TeamCSCV/Project-Orologio/Individual/Audio Output (Chathushka)/2nd Stage/Solid Works/Bouton poussoir.SLDPRT

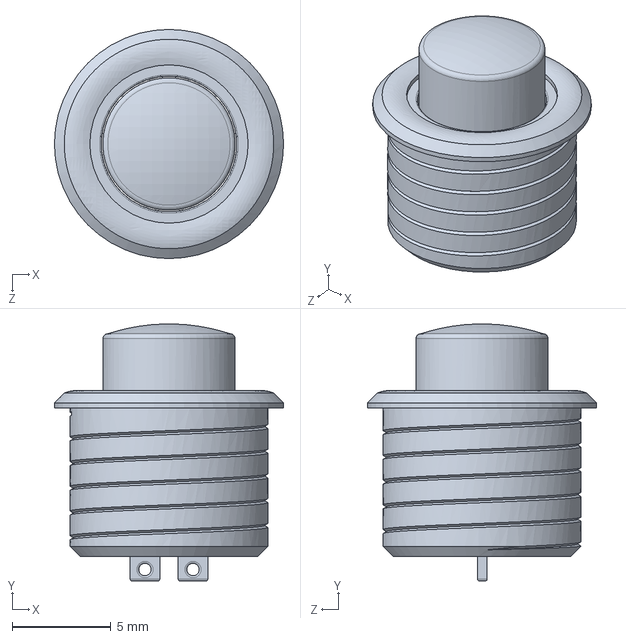
[picture p15: CAD file, 2021-05-29]
Individual/Audio Output (Chathushka)/2nd Stage/Solid Works/Bouton poussoir.SLDPRT
11.6 x 13.0 x 11.6 mm
