TeamCSCV/Project-Orologio/Group/PCB and Schematic/PCB_Project/Models/BC547-B.step

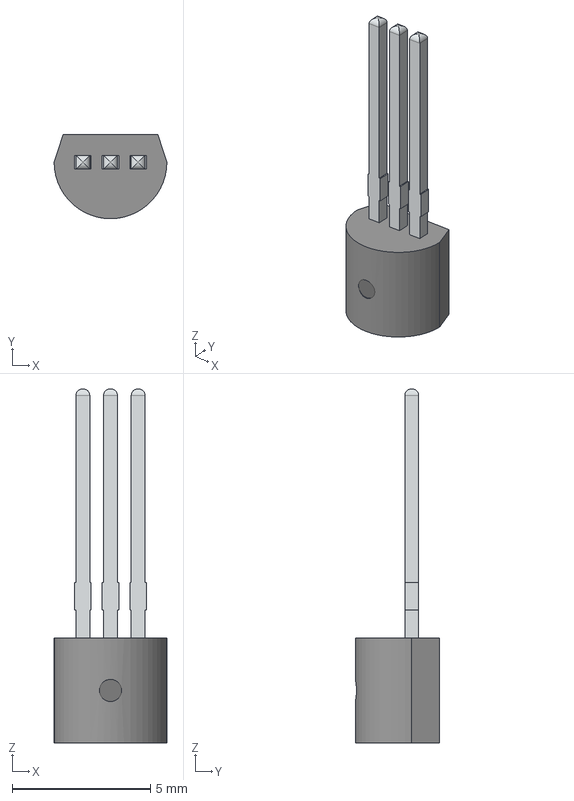
[picture p16: CAD file, 2021-05-29]
Group/PCB and Schematic/PCB_Project/Models/BC547-B.step
4.08 x 3.05 x 12.8 mm
