TeamCSCV/Project-Orologio/Individual/Key Input (Senuri)/Solidworks/9V Battery Holder.SLDPRT

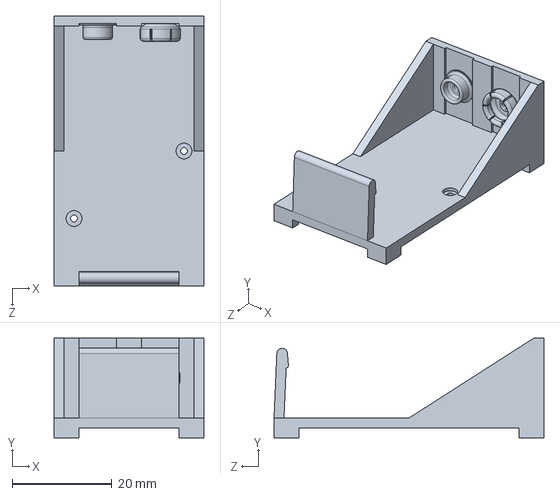
[picture p17: CAD file, 2021-05-29]
Individual/Key Input (Senuri)/Solidworks/9V Battery Holder.SLDPRT
30.0 x 20.0 x 54.0 mm
