TeamCSCV/Project-Orologio/Group/Enclosure/Right Side Arm.STEP

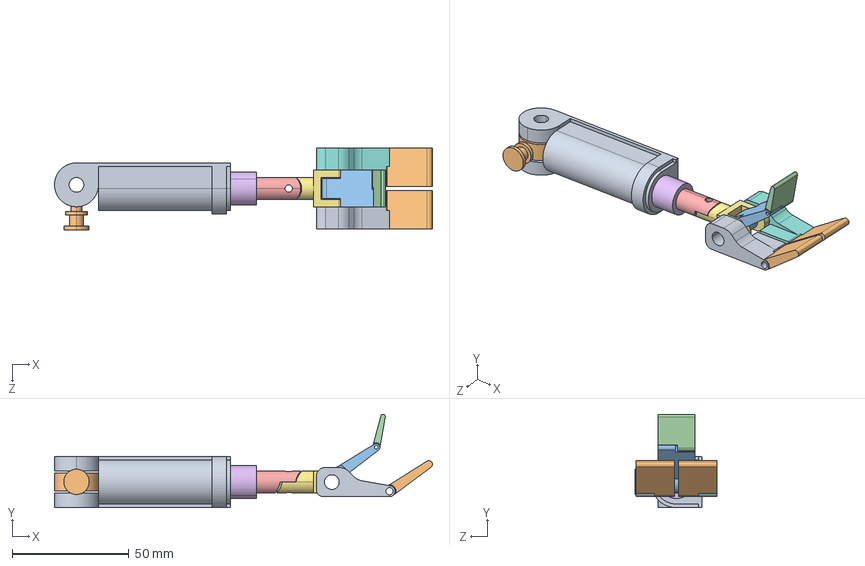
[picture p18: CAD file, 2021-08-09]
Group/Enclosure/Right Side Arm.STEP
161.8 x 40.0 x 34.9 mm
Arm - Main Body
Hand Part 2 x 2
Hand Part 3
Hand Part 4
Hydraulic Arm
Hydraulic Cylinder
Wrist
Hand Part 1
Hand Part 1-2
Sholder
