TeamCSCV/Project-Orologio/Group/PCB and Schematic/PCB_Project/Models/Aluminum_electrolytic_capacitor_radial_D8_H11.5_PinD0.6_Pitch3.5_nominal_black.step

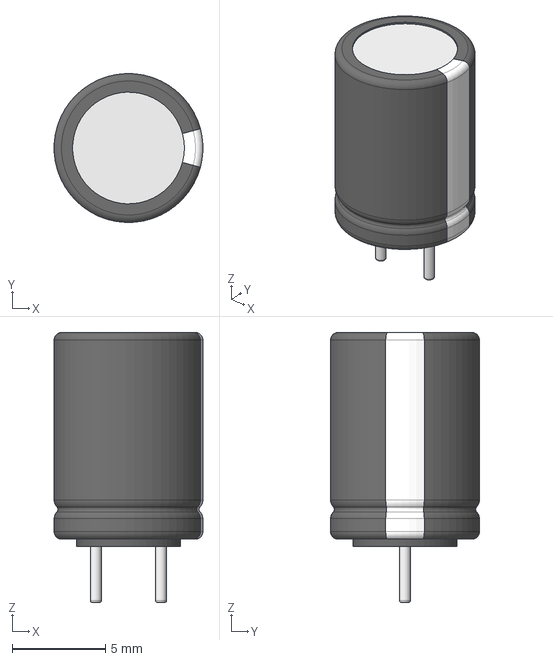
[picture p19: CAD file, 2021-05-29]
Group/PCB and Schematic/PCB_Project/Models/Aluminum_electrolytic_capacitor_radial_D8_H11.5_PinD0.6_Pitch3.5_nominal_black.step
7.99 x 7.99 x 14.5 mm
