TeamCSCV/Project-Orologio/Individual/Key Input (Senuri)/Solidworks/test_bottom.SLDPRT

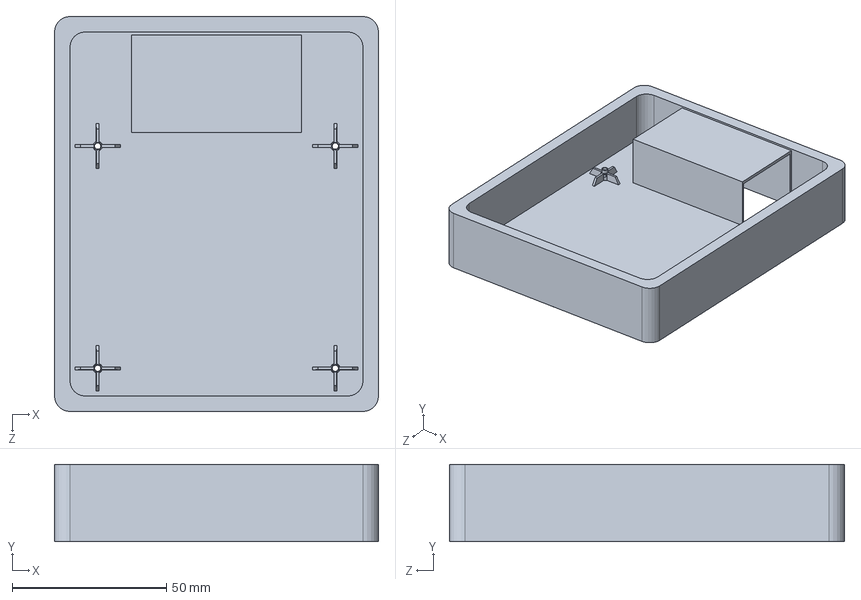
[picture p20: CAD file, 2021-05-29]
Individual/Key Input (Senuri)/Solidworks/test_bottom.SLDPRT
105.0 x 25.0 x 128.0 mm
