TeamCSCV/Project-Orologio/Group/Enclosure/upper part.SLDPRT

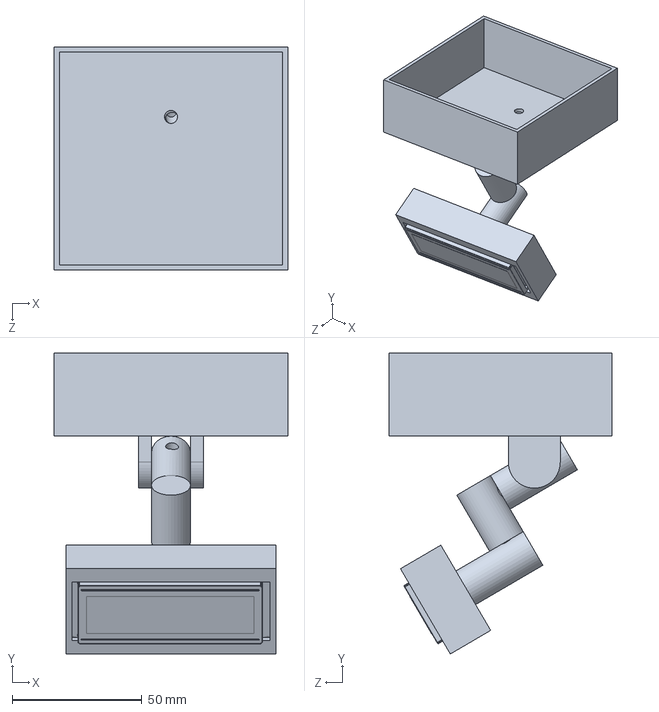
[picture p21: CAD file, 2021-08-09]
Group/Enclosure/upper part.SLDPRT
90.0 x 115.8 x 86.0 mm
