TeamCSCV/Project-Orologio/Group/PCB and Schematic/PCB_Project/Models/L7805ACV.STEP

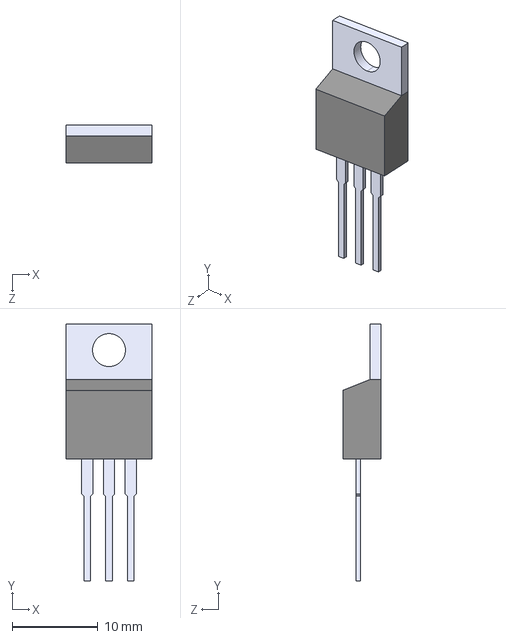
[picture p22: CAD file, 2021-05-29]
Group/PCB and Schematic/PCB_Project/Models/L7805ACV.STEP
10.1 x 30.0 x 4.44 mm
