TeamCSCV/Project-Orologio/Individual/Alarm Timing (Vinuja)/Solidworks enclosure/labProject_micro_top.STEP

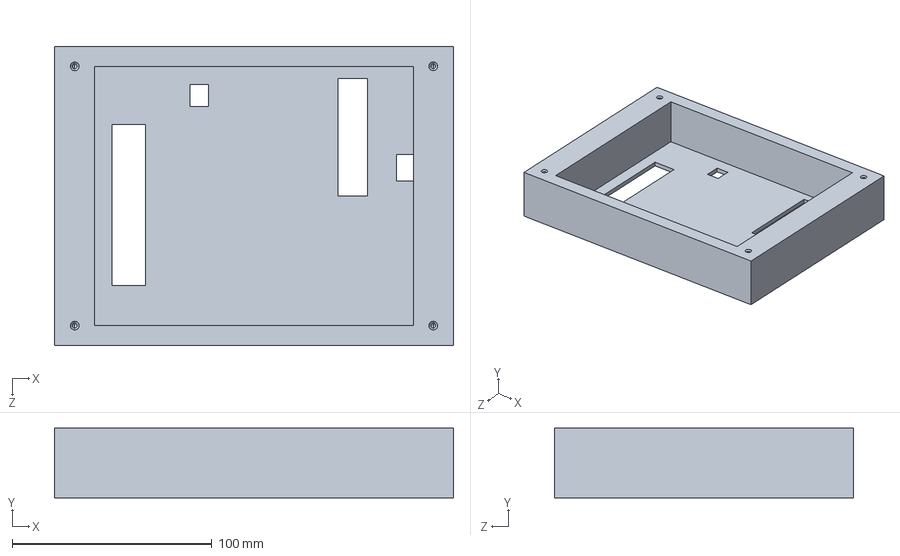
[picture p23: CAD file, 2021-05-29]
Individual/Alarm Timing (Vinuja)/Solidworks enclosure/labProject_micro_top.STEP
200.0 x 35.0 x 150.0 mm
