TeamCSCV/Project-Orologio/Individual/Key Input (Senuri)/Solidworks/Keypad 3x4.STEP

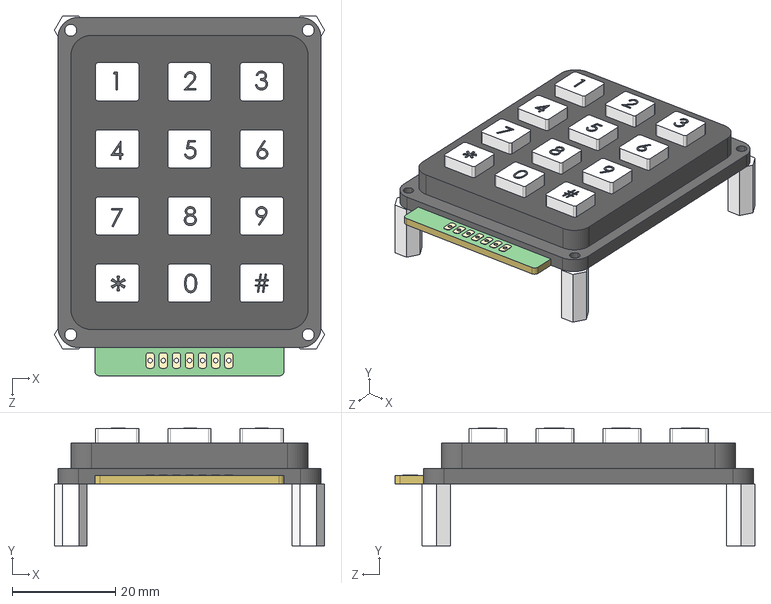
[picture p24: CAD file, 2021-05-29]
Individual/Key Input (Senuri)/Solidworks/Keypad 3x4.STEP
52.4 x 22.8 x 69.8 mm
