TeamCSCV/Project-Orologio/Group/Enclosure/TMB12A05.step.SLDPRT

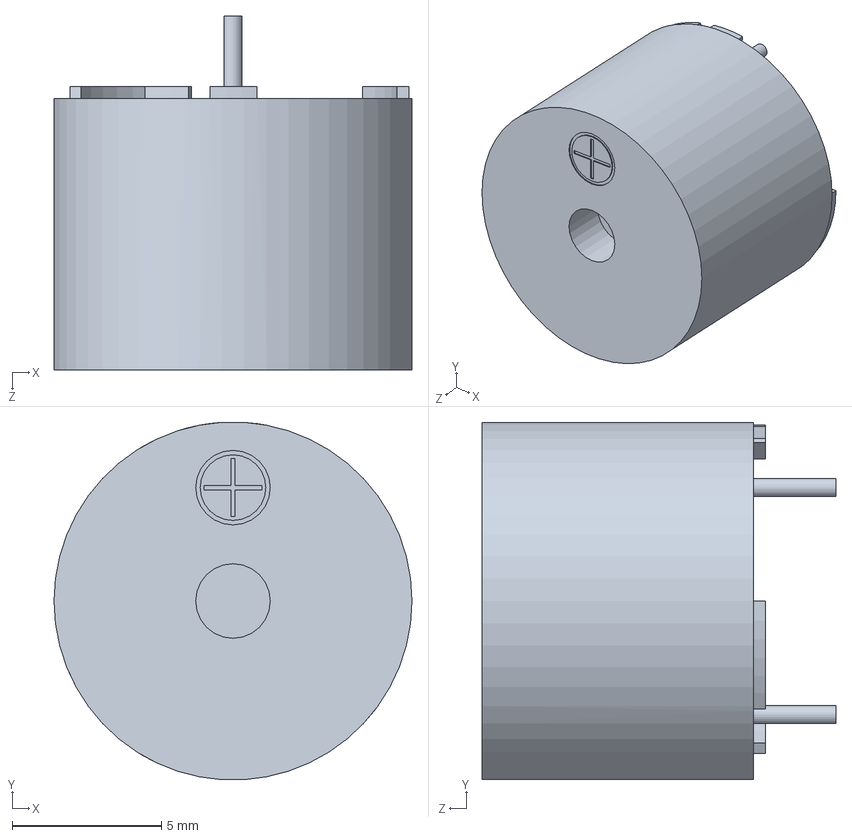
[picture p25: CAD file, 2021-08-09]
Group/Enclosure/TMB12A05.step.SLDPRT
12.0 x 12.0 x 11.9 mm
