TeamCSCV/Project-Orologio/Group/PCB and Schematic/PCB_Project/Models/atmega328p-pu.stp

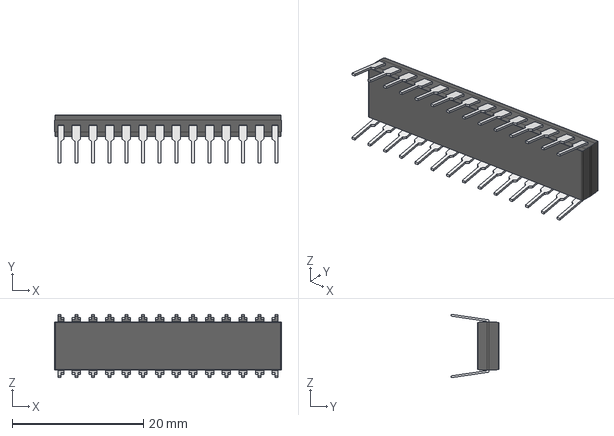
[picture p26: CAD file, 2021-05-29]
Group/PCB and Schematic/PCB_Project/Models/atmega328p-pu.stp
34.6 x 7.30 x 9.68 mm
