TeamCSCV/Project-Orologio/Individual/Alarm Timing (Vinuja)/Solidworks enclosure/labProject_micro_bottom.STEP

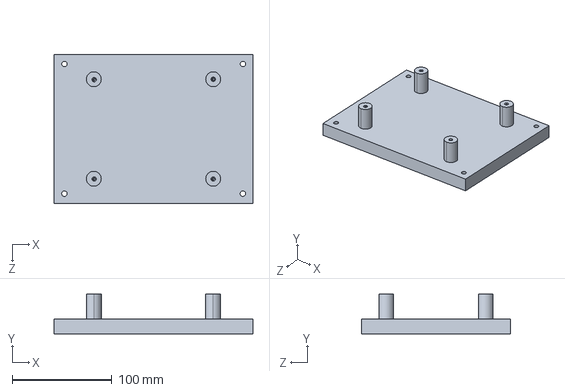
[picture p27: CAD file, 2021-05-29]
Individual/Alarm Timing (Vinuja)/Solidworks enclosure/labProject_micro_bottom.STEP
200.0 x 40.0 x 150.0 mm
