TeamCSCV/Project-Orologio/Group/PCB and Schematic/PCB_Project/Models/1N4001--3DModel-STEP-56544.STEP

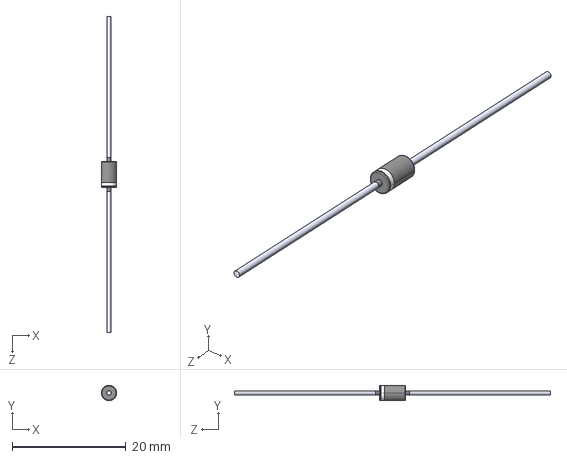
[picture p28: CAD file, 2021-05-29]
Group/PCB and Schematic/PCB_Project/Models/1N4001--3DModel-STEP-56544.STEP
2.69 x 2.69 x 55.4 mm
