TeamCSCV/Project-Orologio/Individual/Display (Chamith)/Solidworks file/button_head.SLDPRT

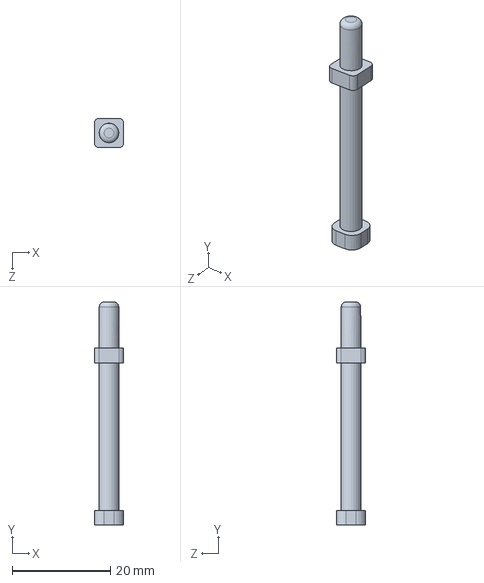
[picture p29: CAD file, 2021-05-31]
Individual/Display (Chamith)/Solidworks file/button_head.SLDPRT
6.00 x 45.5 x 6.00 mm
