TeamCSCV/Project-Orologio/Individual/Display (Chamith)/Solidworks file/top1.SLDPRT

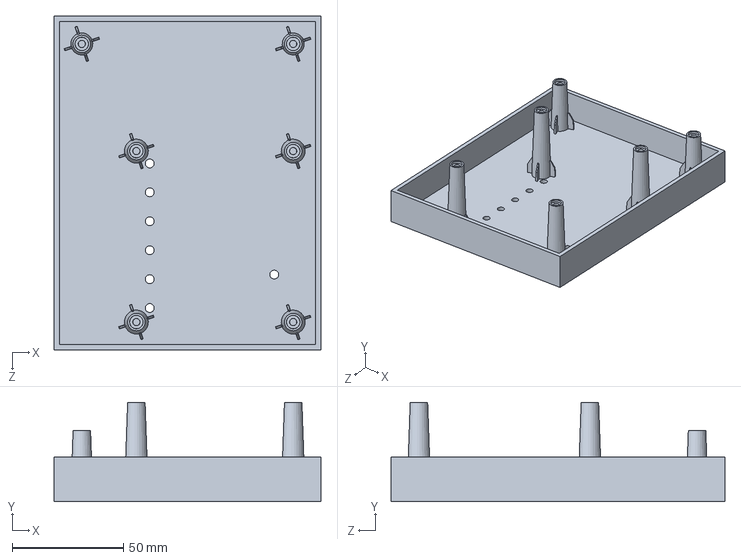
[picture p30: CAD file, 2021-05-31]
Individual/Display (Chamith)/Solidworks file/top1.SLDPRT
120.0 x 44.6 x 150.0 mm
