TeamCSCV/Project-Orologio/Individual/Display (Chamith)/Solidworks file/base1.SLDPRT

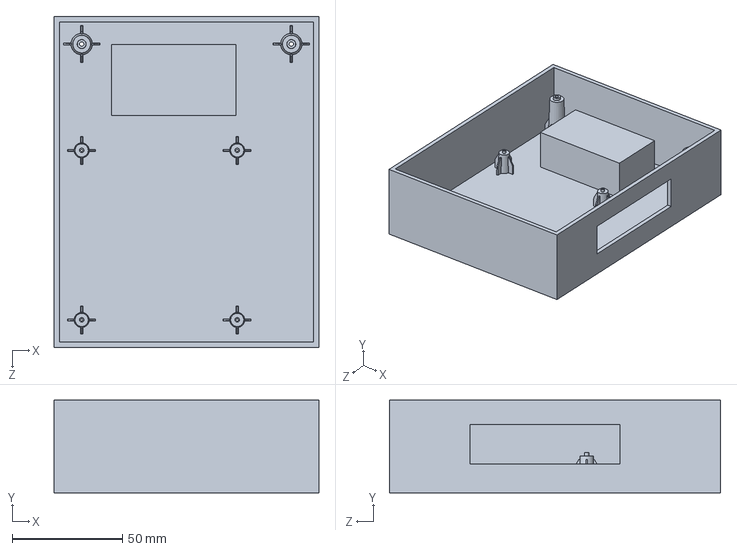
[picture p31: CAD file, 2021-05-31]
Individual/Display (Chamith)/Solidworks file/base1.SLDPRT
120.0 x 42.0 x 150.0 mm
