TeamCSCV/Project-Orologio/Individual/Display (Chamith)/Solidworks file/support to LCD.SLDPRT

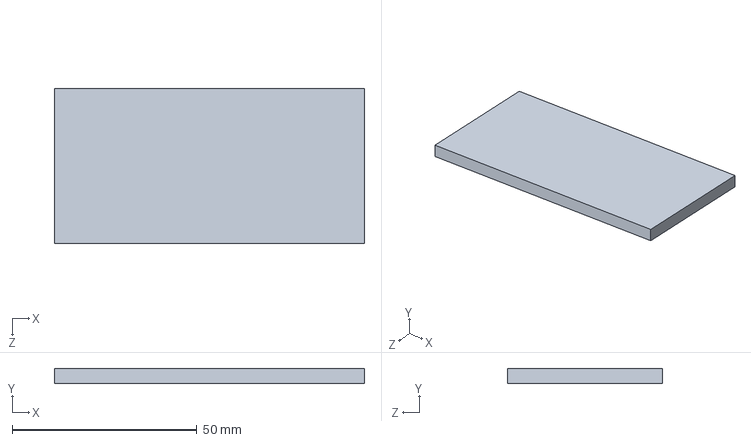
[picture p32: CAD file, 2021-05-31]
Individual/Display (Chamith)/Solidworks file/support to LCD.SLDPRT
84.0 x 4.00 x 42.0 mm
