TeamCSCV/Project-Orologio/Group/Enclosure/wheel.STEP

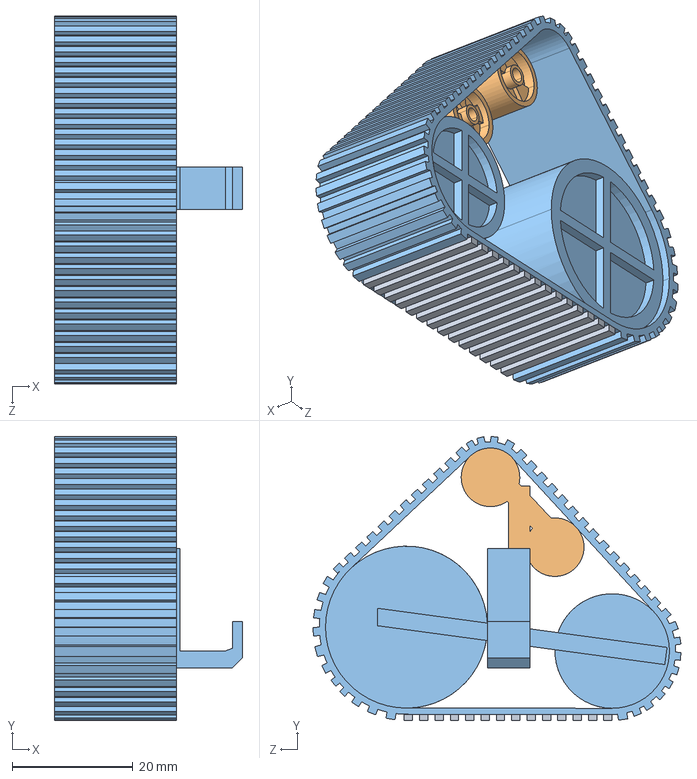
[picture p33: CAD file, 2021-08-04]
Group/Enclosure/wheel.STEP
31.1 x 47.0 x 60.9 mm
