TeamCSCV/Project-Orologio/Group/Enclosure/Matrix Keypad 12 Key (4X3).SLDPRT

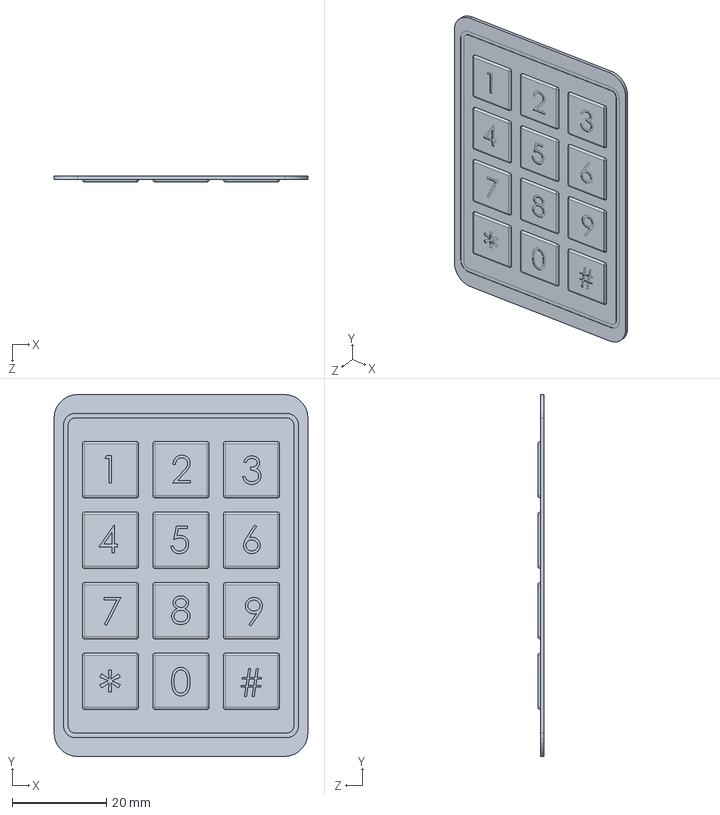
[picture p34: CAD file, 2021-08-04]
Group/Enclosure/Matrix Keypad 12 Key (4X3).SLDPRT
54.0 x 77.0 x 1.31 mm
