TeamCSCV/Project-Orologio/Group/Enclosure/BATTARY HOLDER.SLDPRT

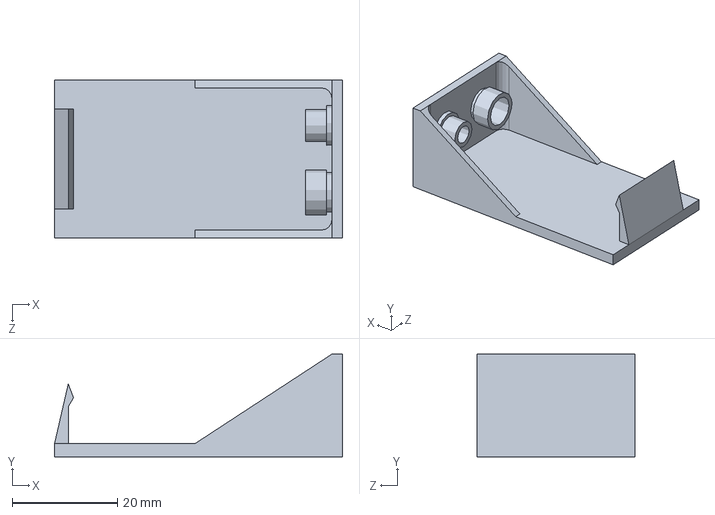
[picture p35: CAD file, 2021-05-29]
Group/Enclosure/BATTARY HOLDER.SLDPRT
54.6 x 19.5 x 30.0 mm
