TeamCSCV/Project-Orologio/Group/Final Product/AlarmTiming/ds1307.cpp

#ifndef DS1307_H
#define DS1307_H
#define __DELAY_BACKWARD_COMPATIBLE__
#ifndef F_CPU
#define F_CPU 1000000UL
#endif

#include <avr/io.h>
#include "ds1307.h"
#include "i2cmaster.h"
#include "util/delay.h"
#define DS1307_ADDRESS 0xD0




uint8_t ds1307_dec2bcd(uint8_t val) {
	return val + 6 * (val / 10);
}
uint8_t ds1307_bcd2dec(uint8_t val) {
	return val - 6 * (val >> 4);
}
void ds1307_init() {
	i2c_init();
	_delay_us(10);
}
void ds1307_setdate(uint8_t year, uint8_t month, uint8_t day, uint8_t dayofweek, uint8_t hour, uint8_t minute, uint8_t second) {
	

	i2c_start_wait(DS1307_ADDRESS | I2C_WRITE);
	i2c_write(0x00);
	i2c_write(ds1307_dec2bcd(second));
	i2c_write(ds1307_dec2bcd(minute));
	i2c_write(ds1307_dec2bcd(hour));
	i2c_write(ds1307_dec2bcd(dayofweek));
	i2c_write(ds1307_dec2bcd(day));
	i2c_write(ds1307_dec2bcd(month));
	i2c_write(ds1307_dec2bcd(year));
	i2c_write(0x00);
	i2c_stop();
}
void ds1307_getdate(uint8_t *year, uint8_t *month, uint8_t *day,uint8_t *dayofweek, uint8_t *hour, uint8_t *minute, uint8_t *second) {
	i2c_start_wait(DS1307_ADDRESS | I2C_WRITE);
	i2c_write(0x00);
	i2c_stop();

	i2c_rep_start(DS1307_ADDRESS | I2C_READ);
	*second = ds1307_bcd2dec(i2c_readAck() & 0x7F);
	*minute = ds1307_bcd2dec(i2c_readAck());
	*hour = ds1307_bcd2dec(i2c_readAck());
	*dayofweek = ds1307_bcd2dec(i2c_readAck());
	*day = ds1307_bcd2dec(i2c_readAck());
	*month = ds1307_bcd2dec(i2c_readAck());
	*year = ds1307_bcd2dec(i2c_readNak());
	i2c_stop();
}
#endif
